ndremferraz/videogame/videogame/character_images.h

#define CHARACTER_WIDTH 8
#define CHARACTER_HEIGTH 8


uint8_t player_img[] = { 0b10000000, 0b01010100, 0b00111111, 0b01010100, 0b10000000, 0b00000000, 0b00111000, 0b00000000};

uint8_t player_img_shooting_right[] = {0b10000000, 0b01010100, 0b00111111, 0b01010100, 0b10000000, 0b00000000, 0b00111000, 0b00010000};

uint8_t player_img_shooting_down[] = {0b10000000, 0b01010100, 0b00111111, 0b01010100, 0b10000000, 0b00000000, 0b10111000, 0b00000000};

uint8_t enemy1_img[] = { 0b00000000, 0b01011110, 0b00110100, 0b01011111, 0b00110101, 0b01011110, 0b00000000, 0b00000000};

uint8_t enemy2_img[] = { 0b01000000, 0b00101110, 0b00011011, 0b00101111, 0b00011011, 0b00101110, 0b01000000, 0b00000000};
